rysiu2007/Class-D-amplifier/Simulation/ClassDAmp.asc

C1: cap; 1.1n; Rser=600m
C2: cap; 1.0n; Rser=600m
C3: cap; 100p; V=100 Irms=364m Rser=0.268918 Lser=0
C4: cap; 100n
C5: cap; 1n
C8: cap; 100n
C9: cap; 1n
C10: cap; 100n
C11: cap; 10µ
C12: cap; 100p
C13: cap; 100p
C14: cap; 1n
C15: cap; 100n
C16: cap; 100n
C19: cap; 100n
C20: cap; 100p
C21: cap; 100p
C22: cap; 1µ
C23: cap; 10n
D1: diode; BAT54HY
D2: diode; BAT54HY
D3: diode
D4: diode; BAT54HY
D5: diode; BAT54HY
D6: diode
L1: ind; 15µ
L2: cap; 1µ
L3: ind; 15µ
M1: nmos; IPD135N03L
M2: nmos; IPD135N03L
M3: nmos; IPD135N03L
M4: nmos; IPD135N03L
Q1: npn; BC547B
Q2: npn; BC547B
Q3: npn
Q4: npn; BC547B
Q5: npn; BC547B
Q6: npn; BC847B
Q7: npn; BC547B
Q8: npn; BC547B
Q9: npn; BC547B
Q10: pnp; BC327-25
Q11: npn; BC817-40
Q12: pnp; BC327-25
Q13: npn; BC817-40
Q14: npn; BC817-40
Q15: npn; BC817-40
Q16: pnp; BC327-25
Q17: npn; BC817-40
Q18: pnp; BC327-25
Q19: npn; BC817-40
Q20: npn; BC817-40
Q21: npn; BC817-40
R1: res; 1k; tol=1 pwr=0.25
R2: res; 1k; tol=1 pwr=0.25
R3: res; 6.7k; tol=1 pwr=0.25
R4: res; 6.7k; tol=1 pwr=0.25
R5: res; 100; tol=1 pwr=0.25
R6: res; 1k; tol=1 pwr=0.25
R7: res; 470; tol=1 pwr=0.25
R8: res; 470; tol=1 pwr=0.25
R9: res; 1k; tol=1 pwr=0.25
R10: res; 50k; tol=1 pwr=0.25
R11: res; 5k
R12: res; 330; tol=1 pwr=0.25
R13: res; 1k
R14: res; 1k
R15: res; 5k
R16: res; 5k
R17: res; 100
R18: res; 10k
R19: res; 10k
R20: res; 240
R21: res; 6.7k
R22: res; 620
R23: res; 1k
R24: res; 5k
R25: res; 1k
R26: res; 150
R27: res; 100k
R28: res; 200
R29: res; 1k
R30: res; 0.01
R31: res; 100k
R32: res; 100k
R33: res; 47k
R34: res; 1k
R35: res; 10k
R36: res; 240
R37: res; 6.7k
R38: res; 620
R39: res; 10k
R40: res; 150
R41: res; 200
R42: res; 0.01
R43: res; 1k
R44: res; 1k
R45: res; 10k
R46: res; 10k
R47: res; 4
R48: res; 0.01
R49: res; 0.01
V1: voltage; 12
V2: voltage; SINE(6 1.1 1000); AC 1 0
Named nets: 0
.tran 0 100ms 0 10n startup
.fra tstart=1 dtmax=10u
.ac dec 100 10 20k
.step param freq list 100 1k 10k 20k
.param freq=1k
